mentako-ya/mtk/mtk/remap_img/mtk64_db_keymap.png

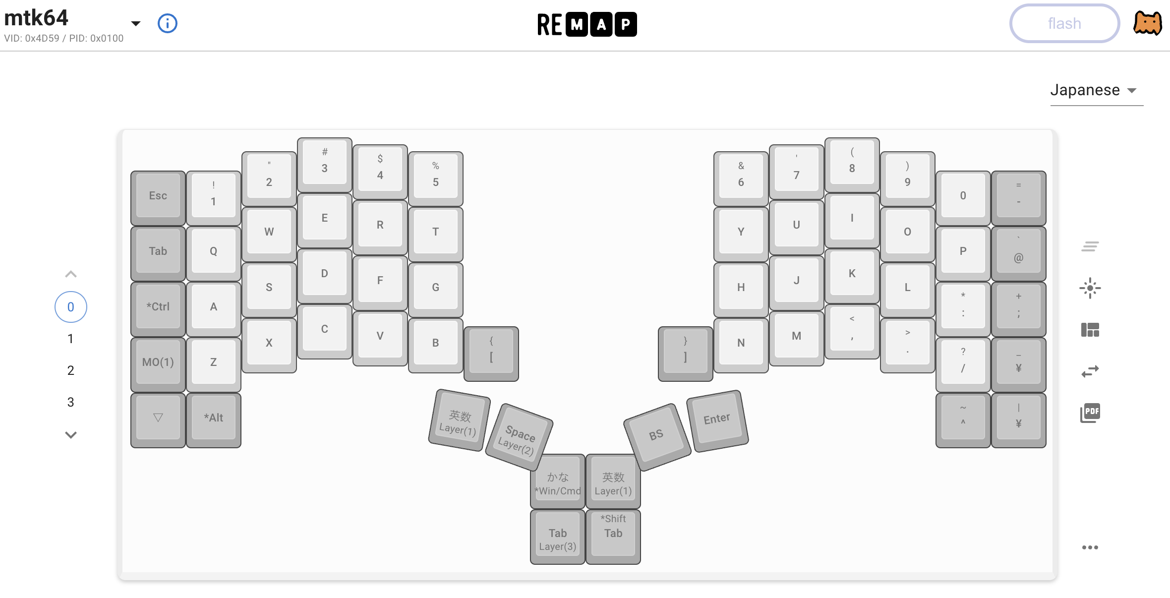
mtk/remap_img/mtk64_db_keymap.png
