mentako-ya/mtk/mtk/remap_img/mtk64_rb_keymap.png

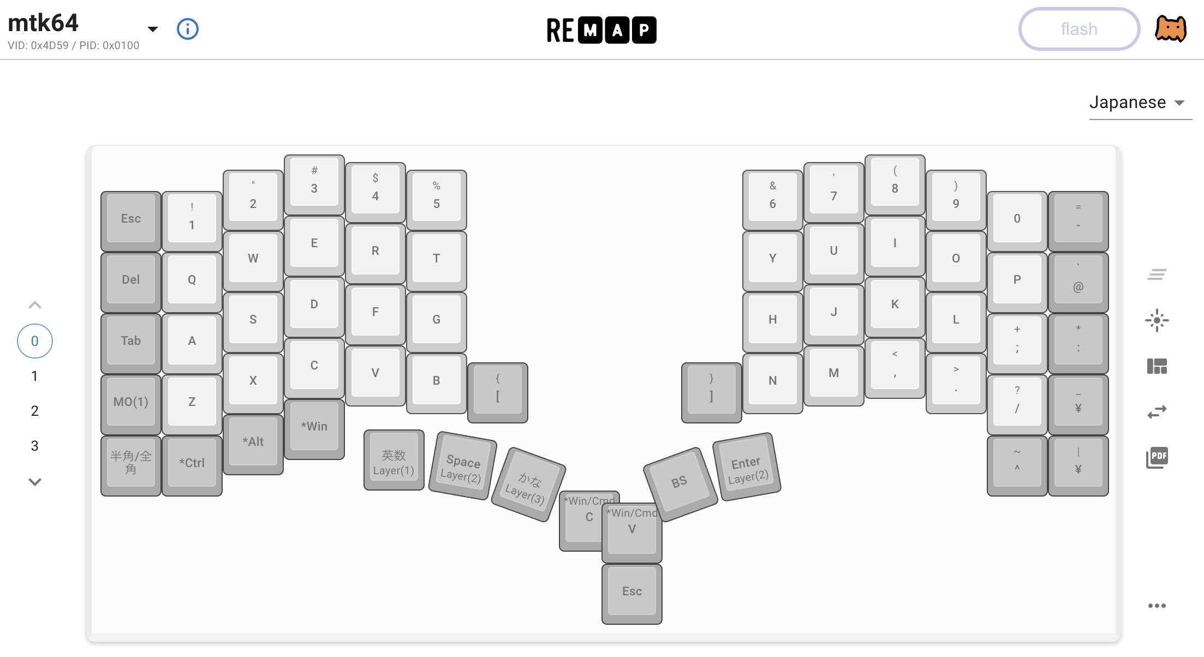
mtk/remap_img/mtk64_rb_keymap.png
