mentako-ya/mtk/mtk/remap_img/mtk64e_keymap.png

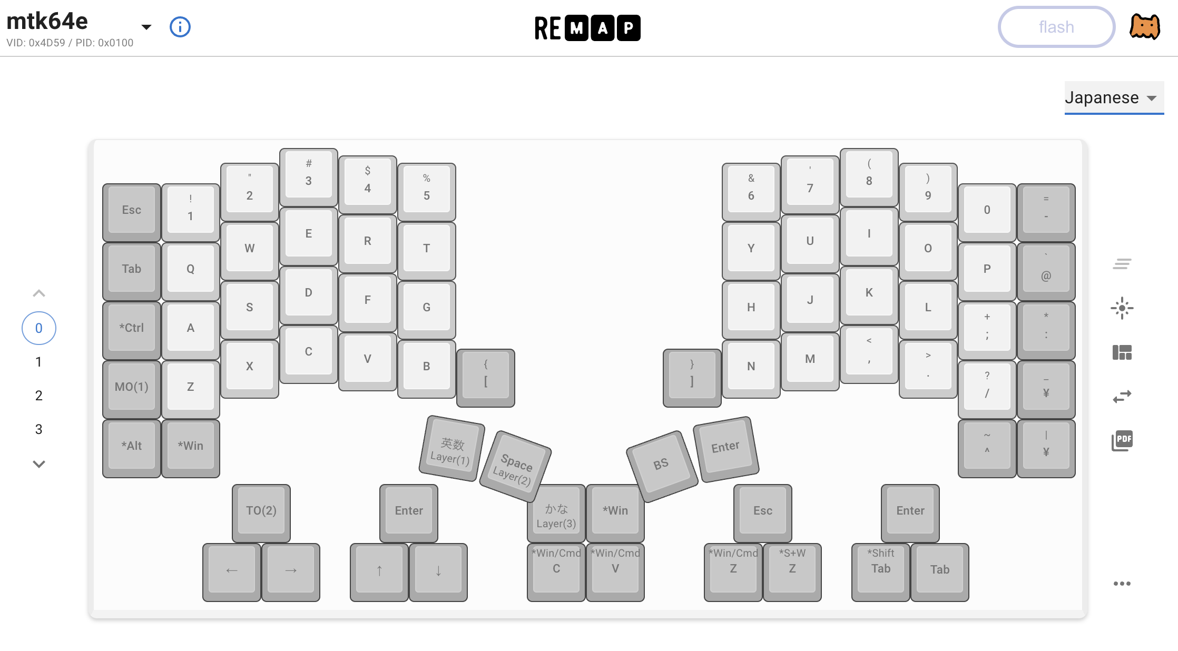
mtk/remap_img/mtk64e_keymap.png
