mentako-ya/mtk/mtk/remap_img/remap_1.png

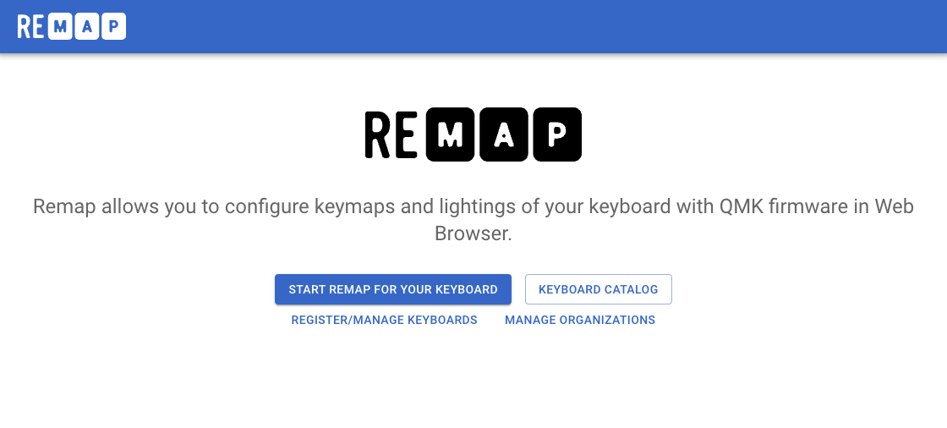
mtk/remap_img/remap_1.png
