mentako-ya/mtk/mtk/remap_img/remap_2.png

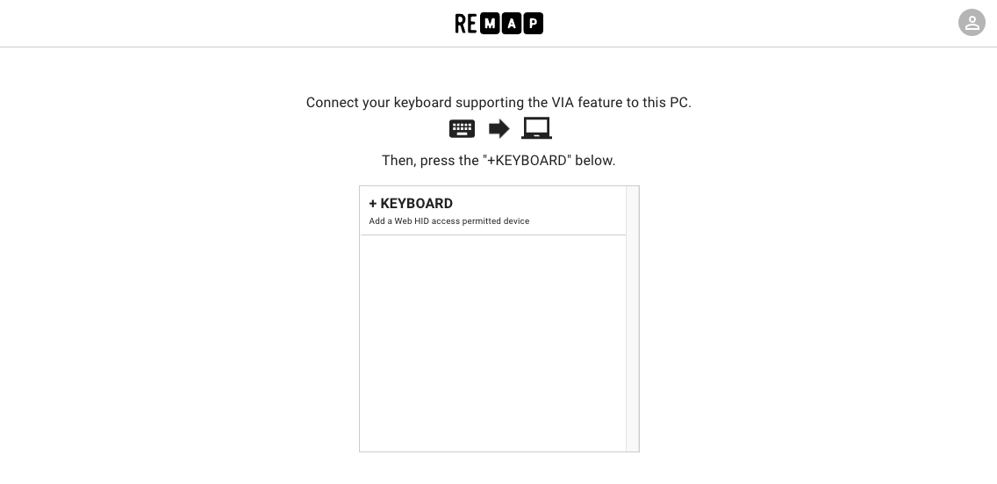
mtk/remap_img/remap_2.png
