mentako-ya/mtk/mtk/remap_img/remap_3.png

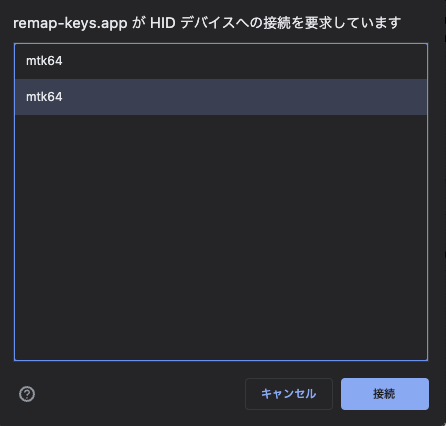
mtk/remap_img/remap_3.png
