mentako-ya/mtk/mtk/remap_img/remap_4.png

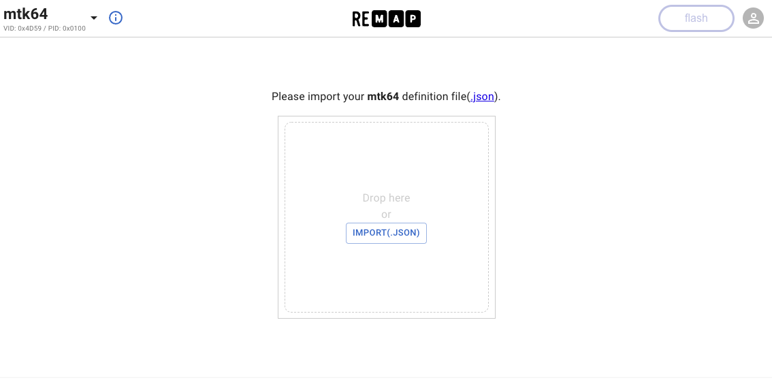
mtk/remap_img/remap_4.png
