mentako-ya/mtk/mtk/web_updater_img/1_select_file.png

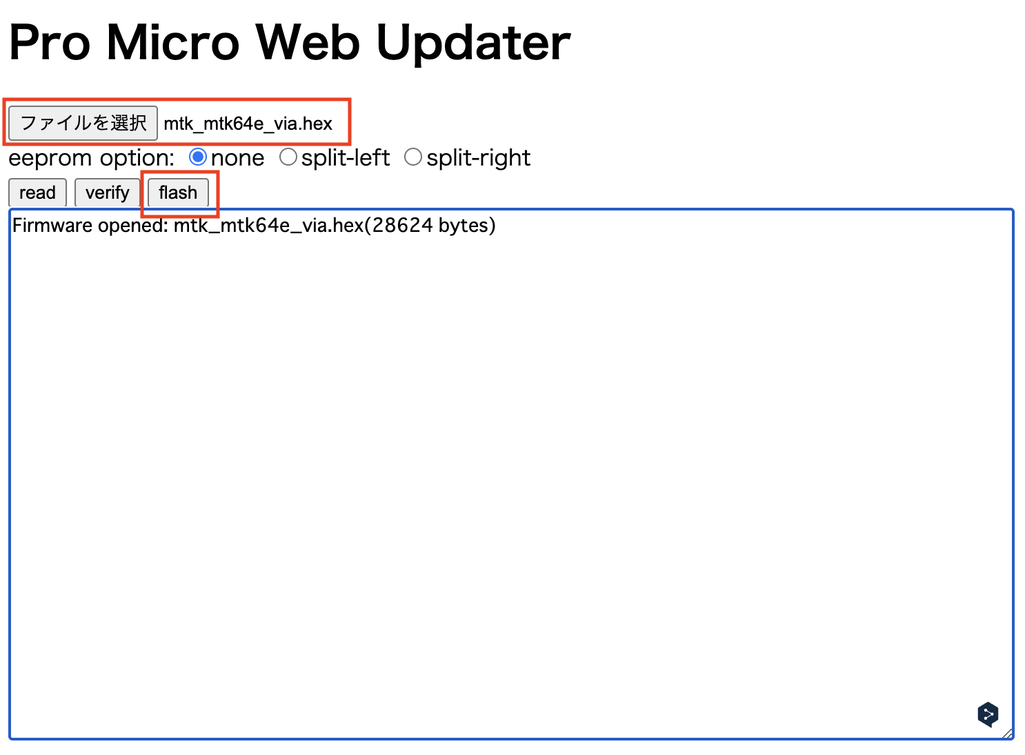
mtk/web_updater_img/1_select_file.png
