mentako-ya/mtk/mtk/web_updater_img/2_select_device.png

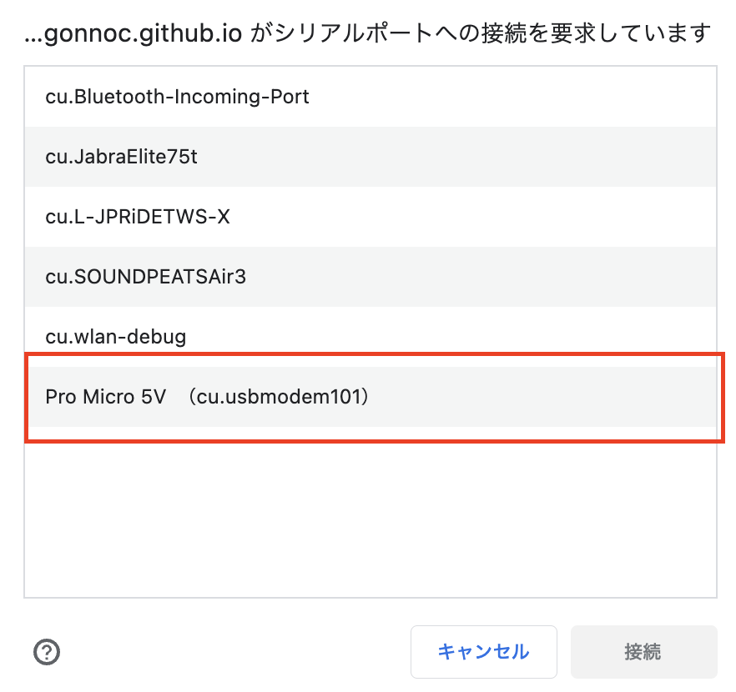
mtk/web_updater_img/2_select_device.png
