mentako-ya/mtk/mtk/design/mtk64elt_STL/rev3/mtk64el_rev3_proMicroCase_RH.stl

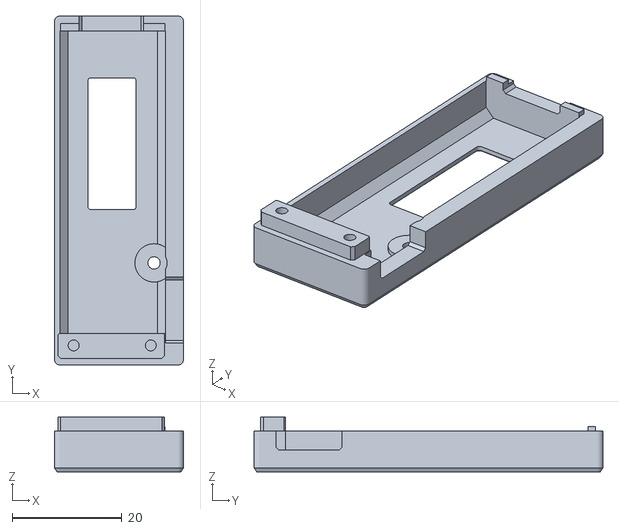
[picture p39: CAD file, 2024-02-10]
mtk/design/mtk64elt_STL/rev3/mtk64el_rev3_proMicroCase_RH.stl
23.5 x 63.6 x 10.0
