mentako-ya/mtk/mtk/design/mtk64elt_STL/rev3/mtk64el_rev3_encoderCase_LH.stl

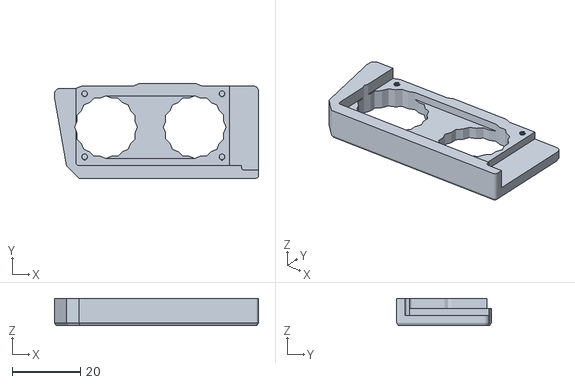
[picture p40: CAD file, 2024-02-10]
mtk/design/mtk64elt_STL/rev3/mtk64el_rev3_encoderCase_LH.stl
59.8 x 27.7 x 8.00
