mentako-ya/mtk/mtk/design/mtk64elp_STL/mtk64_EncoderCase_RH_rev2 v26.stl

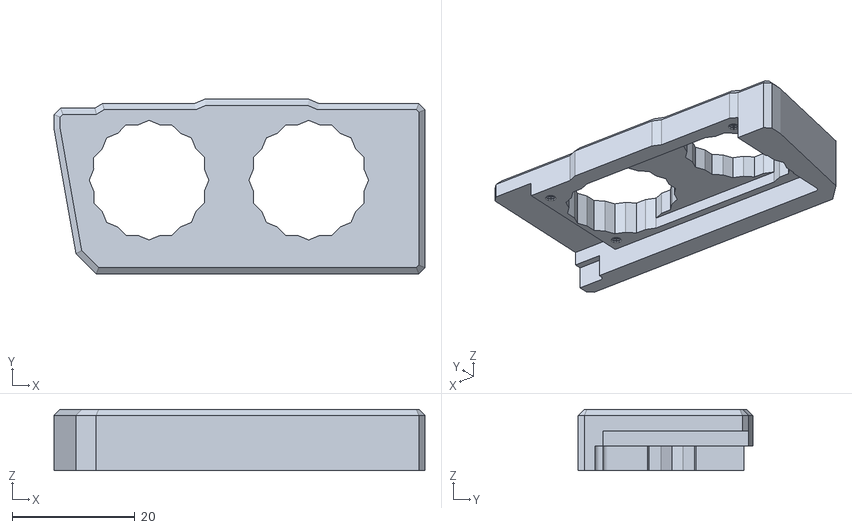
[picture p41: CAD file, 2022-10-26]
mtk/design/mtk64elp_STL/mtk64_EncoderCase_RH_rev2 v26.stl
60.4 x 28.4 x 10.0
