mentako-ya/mtk/mtk/design/mtk64elt_STL/rev3/mtk64el_rev3_bottomPlateEncoderSide_RH.stl

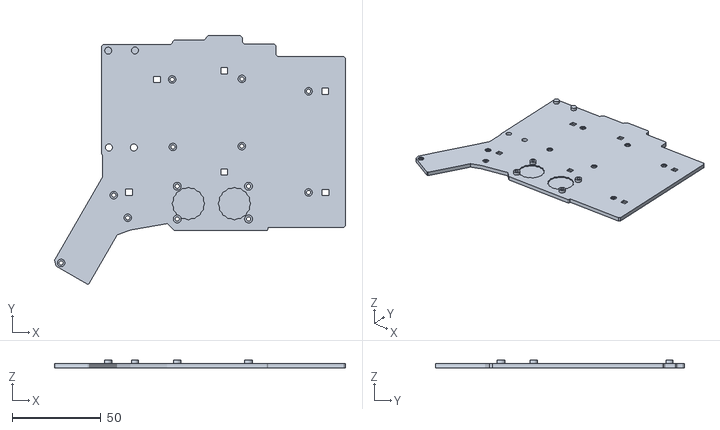
[picture p42: CAD file, 2024-02-10]
mtk/design/mtk64elt_STL/rev3/mtk64el_rev3_bottomPlateEncoderSide_RH.stl
164.4 x 140.5 x 4.75
