mentako-ya/mtk/mtk/design/mtk64elp_STL/mtk64_BP_RH_rev2 v22.stl

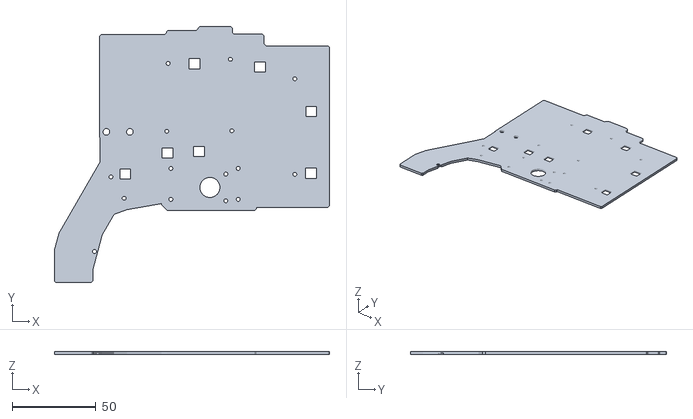
[picture p43: CAD file, 2022-10-26]
mtk/design/mtk64elp_STL/mtk64_BP_RH_rev2 v22.stl
164.5 x 153.4 x 2.00
