mentako-ya/mtk/mtk/design/mtk64elt_STL/rev3/mtk64el_rev3_tent_RH.stl

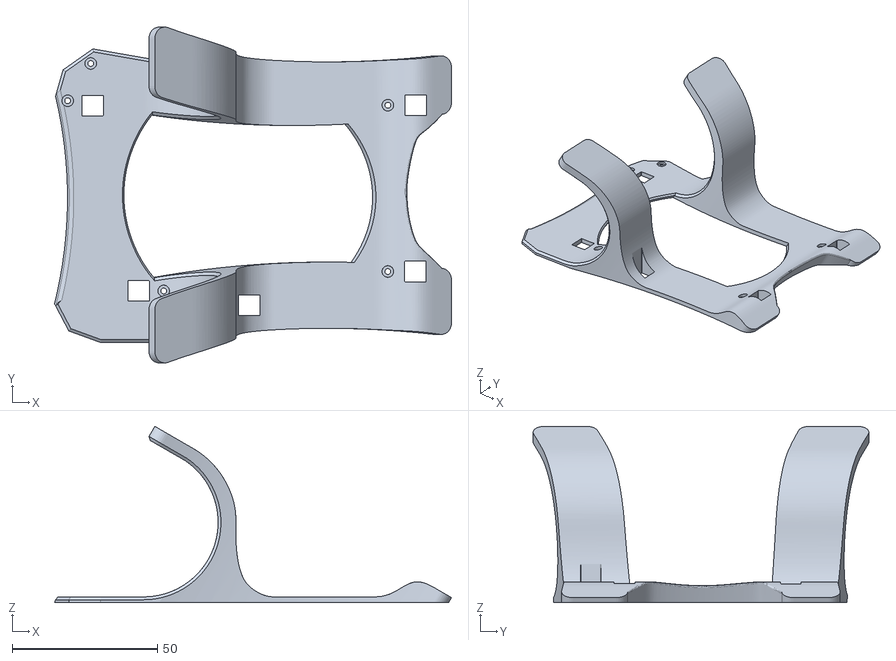
[picture p44: CAD file, 2024-02-10]
mtk/design/mtk64elt_STL/rev3/mtk64el_rev3_tent_RH.stl
136.4 x 115.4 x 60.6
