mentako-ya/mtk/mtk/design/mtk64elt_STL/rev3/EC11N1524402_Knob_16mm.stl

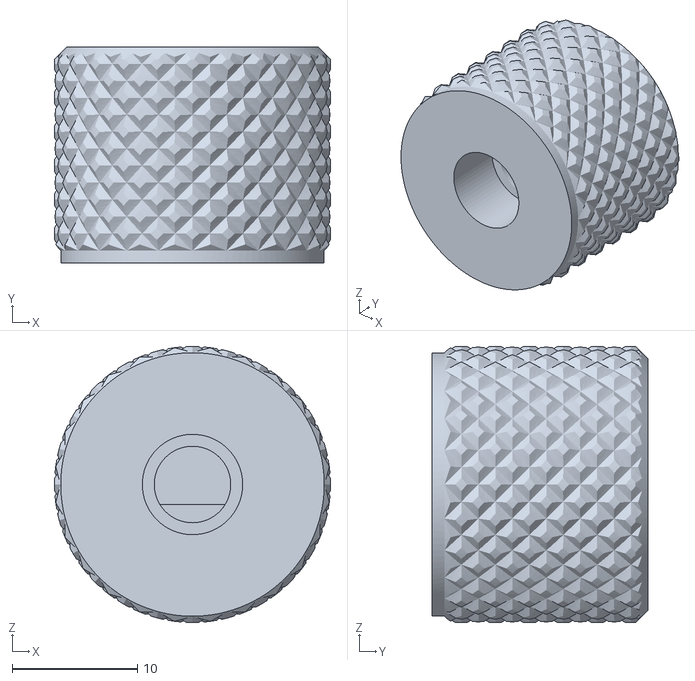
[picture p46: CAD file, 2023-11-15]
mtk/design/mtk64elt_STL/rev3/EC11N1524402_Knob_16mm.stl
22.0 x 17.2 x 22.0
