mentako-ya/mtk/mtk/design/mtk64elt_STL/rev3/EC11N1524402_Knob_13mm.stl

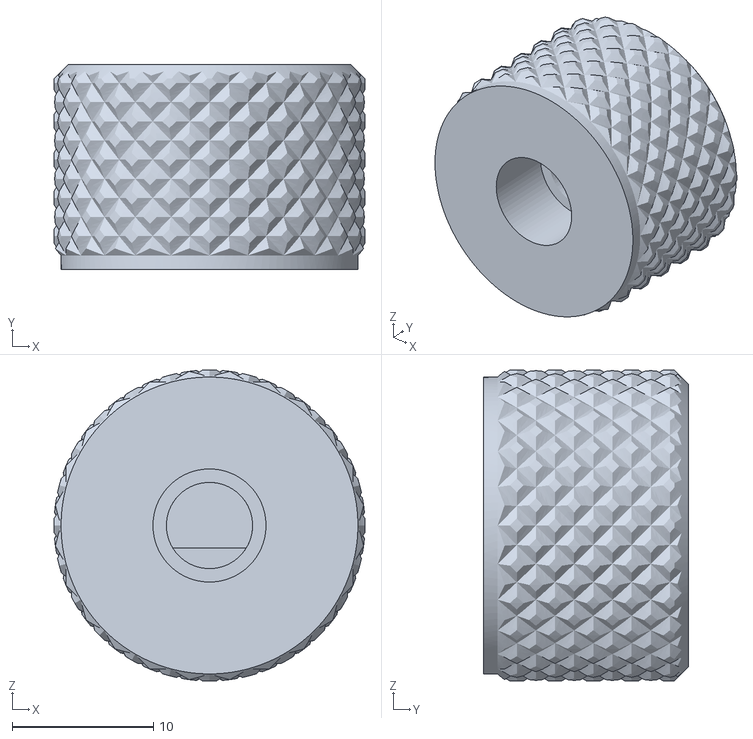
[picture p47: CAD file, 2023-11-15]
mtk/design/mtk64elt_STL/rev3/EC11N1524402_Knob_13mm.stl
22.0 x 14.5 x 22.0
